Aidevig/Bracelet/bracelet/bracelet go-safe.sch

## EAGLE design bracelet/bracelet go-safe.sch (2016-01-29)

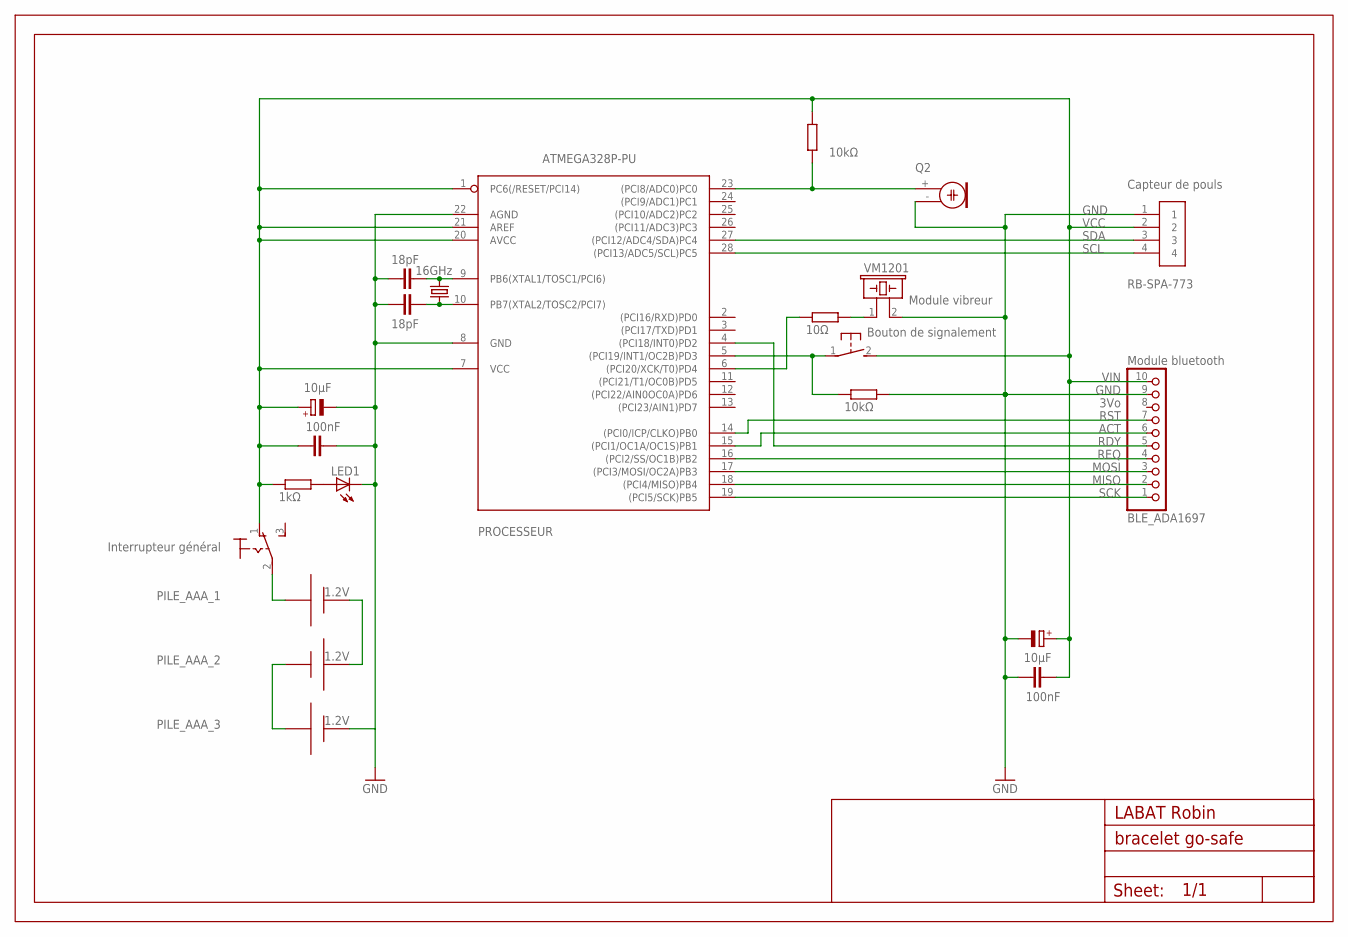
[picture p20: schematic bracelet go-safe.sch]

Parts:
BLE_ADA1697: Module bluetooth; 1X10-BIG
C1, C2: 18pF; C025-024X044
C3, C4: 100nF; C025-024X044
C5, C6: 10µF; 085CS_1AR
FRAME1: A4L-LOC
LED1: LED; SMARTLED-TTW
PILE_AAA_1, PILE_AAA_2, PILE_AAA_3: AAA; 12BH412
PROCESSEUR: ATMEGA328P-PU; DIL28-3
Q1: 16GHz; 86SMX
Q2: ELECTRET; 9.7ELECTRET
R1: 10Ω; 0204V
R2, R4: 10kΩ; 0204V
R3: 1kΩ; 0204V
RB-SPA-773: Capteur de pouls; 1X04-3.5MM
S2: Bouton de signalement; B3F-31XX
S3: Interrupteur général; 320-916
VM1201: Module vibreur; B/C14S

Connections:
GND: BLE_ADA1697.9, C1.1, C2.1, C3.2, C4.2, C5.-, C6.-, LED1.C@1 (C), PILE_AAA_3.+, PROCESSEUR.8 (GND), PROCESSEUR.22 (AGND), Q2.- (1), R2.2, RB-SPA-773.1, VM1201.2
unnamed: PILE_AAA_2.+, PILE_AAA_3.-
unnamed: PILE_AAA_1.+, PILE_AAA_2.-
unnamed: BLE_ADA1697.10, C3.1, C4.1, C5.+, C6.+, PROCESSEUR.1 (PC6(/RESET/PCI14)), PROCESSEUR.7 (VCC), PROCESSEUR.20 (AVCC), PROCESSEUR.21 (AREF), R3.1, R4.2, RB-SPA-773.2, S2.2 (S), S3.1 (O)
unnamed: C2.2, PROCESSEUR.10 (PB7(XTAL2/TOSC2/PCI7)), Q1.1
unnamed: C1.2, PROCESSEUR.9 (PB6(XTAL1/TOSC1/PCI6)), Q1.4 (2)
unnamed: BLE_ADA1697.1, PROCESSEUR.19 ((PCI5/SCK)PB5)
unnamed: PILE_AAA_1.-, S3.2
unnamed: BLE_ADA1697.2, PROCESSEUR.18 ((PCI4/MISO)PB4)
unnamed: BLE_ADA1697.3, PROCESSEUR.17 ((PCI3/MOSI/OC2A)PB3)
unnamed: BLE_ADA1697.4, PROCESSEUR.16 ((PCI2/SS/OC1B)PB2)
unnamed: BLE_ADA1697.5, PROCESSEUR.4 ((PCI18/INT0)PD2)
unnamed: BLE_ADA1697.7, PROCESSEUR.14 ((PCI0/ICP/CLKO)PB0)
unnamed: BLE_ADA1697.6, PROCESSEUR.15 ((PCI1/OC1A/OC1S)PB1)
unnamed: PROCESSEUR.27 ((PCI12/ADC4/SDA)PC4), RB-SPA-773.3
unnamed: R1.2, VM1201.1
unnamed: PROCESSEUR.6 ((PCI20/XCK/T0)PD4), R1.1
unnamed: PROCESSEUR.28 ((PCI13/ADC5/SCL)PC5), RB-SPA-773.4
unnamed: LED1.A@1 (A), R3.2
unnamed: PROCESSEUR.5 ((PCI19/INT1/OC2B)PD3), R2.1, S2.1
unnamed: PROCESSEUR.23 ((PCI8/ADC0)PC0), Q2.+ (2), R4.1
